jmlzone/PiPtr/doc/IMG_1385.jpg

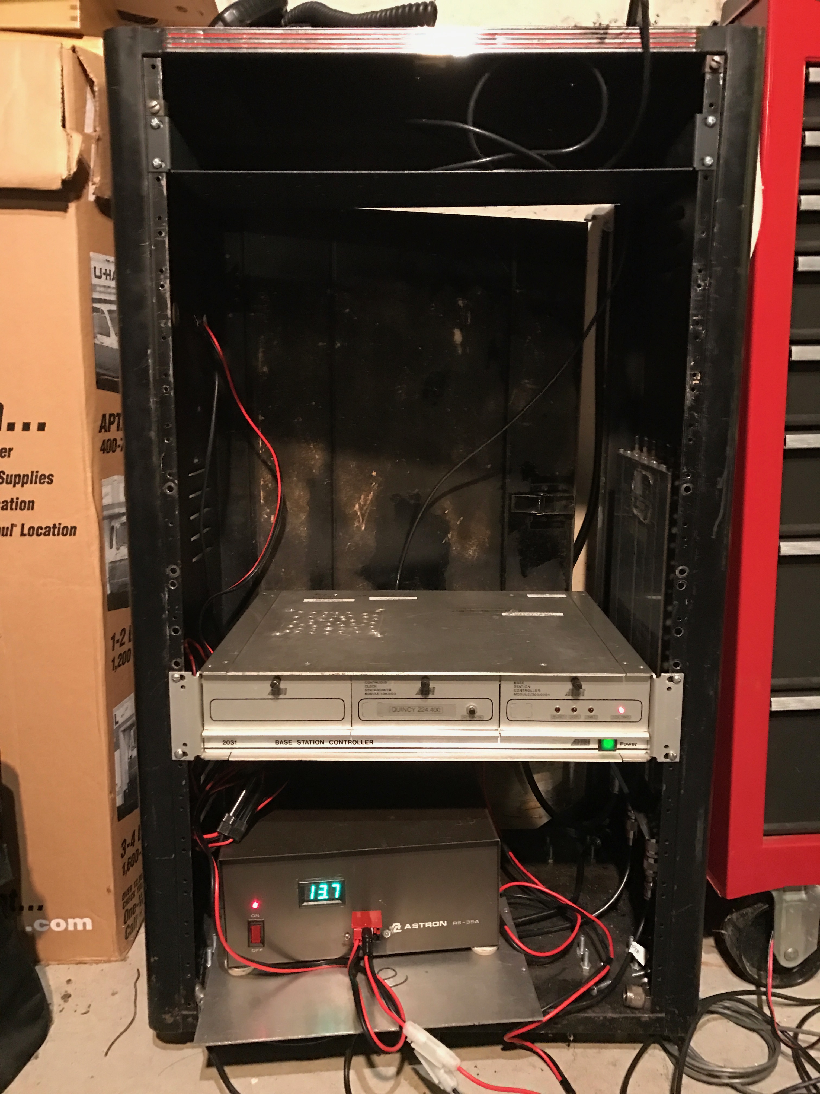
doc/IMG_1385.jpg
