jmlzone/PiPtr/doc/IMG_1389.jpg

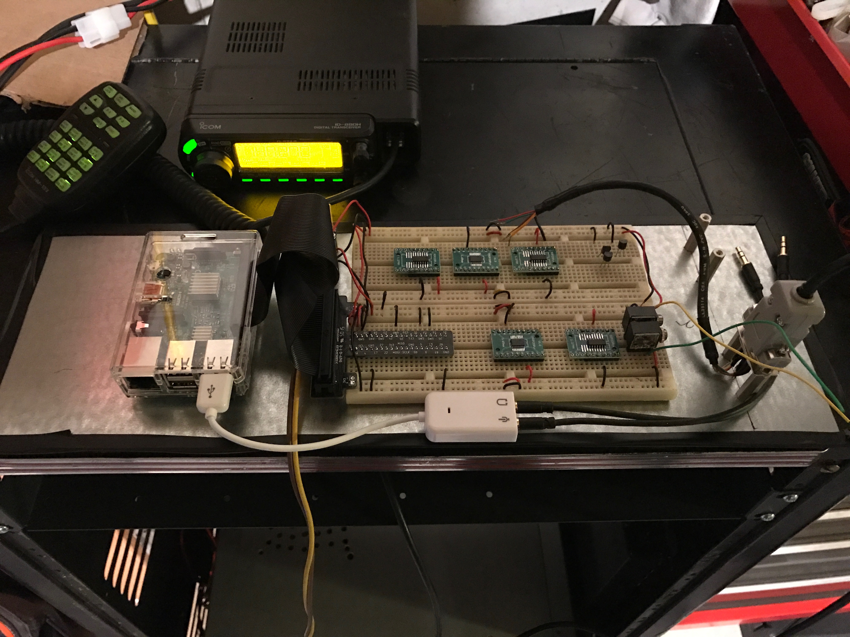
doc/IMG_1389.jpg
