jmlzone/PiPtr/doc/IMG_1816.jpg

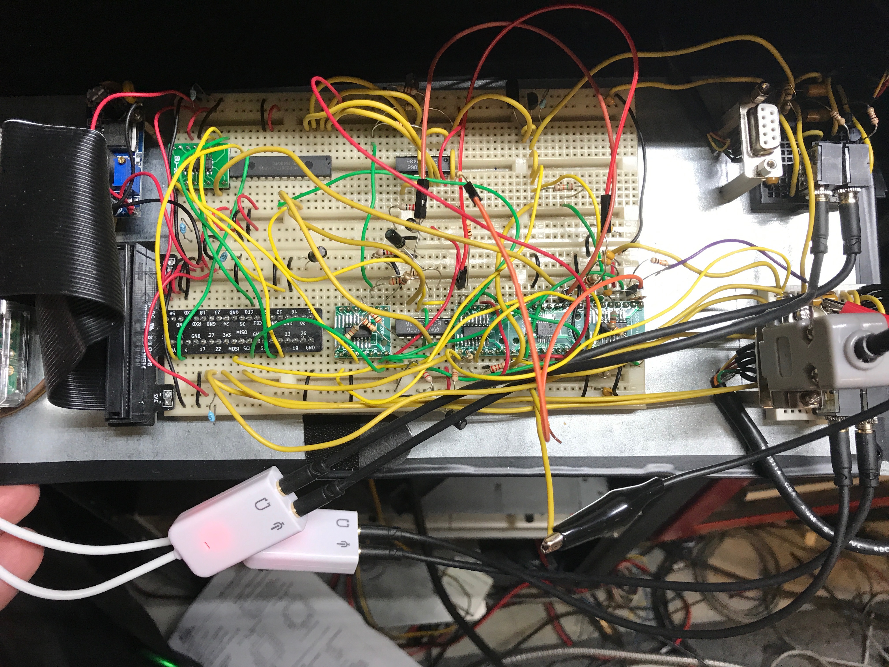
doc/IMG_1816.jpg
