jmlzone/PiPtr/python/radioPort.py

import time
import socket
import os.path
import RPi.GPIO as GPIO
import subprocess
import sys
import re
import signal
import threading
#import tail
import rptFsm
from logit import logit

from multiprocessing import Process, Value, Array, Queue
class tx:
    """ class describing a transmitter """
    def __init__(self, port):
        self.installPath = os.path.dirname(os.path.realpath(__file__))
        self.port = port # handle to parent
        self.pltone = 100.0
        self.id = "n0call"
        self.tailMsgList =  []
        self.beaconMsgList = []
        self.timeout = 3600 # 1 hour max tx up continously
        self.taildly = 0.5 # seconds
        self.txupdly = 1 # seconds When coming up to beacon, delay bedore sending
        self.hangtime = 1 #seconds
        self.idtime = 300 # seconds
        self.polite = 30
        self.disable = False
        self.TailMessagesDone = False
        self.txPinLvl = 1
        if(self.port.portnum == 1) :
            self.pttPin = 15
            self.txState=self.port.globalState.tx1.setValue
        else :
            self.pttPin = 22
            self.txState=self.port.globalState.tx2.setValue

        GPIO.setmode(GPIO.BOARD)
        GPIO.setup(self.pttPin, GPIO.OUT)
        GPIO.output(self.pttPin,(not self.txPinLvl))
        #self.tail_msg = tail.tail_msg(self.port.card)
        self.pid = False
        self.idPid = False
        self.beepMethod = 2 # 0=none, 1=tone, 2=wave 3=morse
        self.beepTone = "660 5000 30 440 5000 30 1000 5000 30"
        self.tailBeepWav = self.localPath('../sounds/Tink.wav')
        self.defMorseWpm = 20
        self.defMorseTone = 660
        self.defMorseVolume = 5000
        self.beepMorse = "20 440 5000 beep"
        self.xmlvars = ( 'pltone', 'id', 'idtime', 'polite', 'timeout',
                         'taildly', 'hangtime', 'disable', 'txupdly',
                         'txPinLvl', 'beepMethod', 'beepTone',
                         'tailBeepWav', 'beepMorse',
                         'defMorseWpm','defMorseTone','defMorseVolume'
                     ) # data to store in xml config
        self.up = False

    def localPath(self,file) :
        return (os.path.abspath(os.path.join(self.installPath,file)))
    
    def addTailMsg(self, method,msg,cancelable,isid,requeue,alt):
        self.tailMsgList.append((method,msg,cancelable,isid,requeue,alt))
        print("Added tail message %s " % msg)

    def addBeaconMsg(self, method,msg,cancelable,isid,requeue,alt):
        self.beaconMsgList.append((method,msg,cancelable,isid,requeue,alt))
        print("Added beacon message %s " % msg)


    def tx(self) :
        if( not self.disable) :
            #self.port.startPl(pltone)
            #self.port.tx_enable()
            GPIO.output(self.pttPin,self.txPinLvl)
            #self.port.gui.updateTxGui(self.port.portnum,True)
            self.txState(True,'red')
            self.up = True

    def plGen(self) :
        """ Starts this transmitters Pl generator

        not going to worry about the details yet
        """
        print("pl gen on")
    def plStop(self) :
        """ Stops this transmitters Pl generator

       not going to worry about the details yet
       """
        print("pl gen off")
        
    def down(self):
        GPIO.output(self.pttPin,(not self.txPinLvl))
        #self.port.gui.updateTxGui(self.port.portnum,False)
        self.txState(False)
        self.up = False

    def playMsgs(self,msgList) :
        print(" play messages called")
        print(msgList)
        self.cancel = False
        id_played = False
        i=0;
        while(i<len(msgList)) :
            print("i = %d" %i)
            ele = msgList[i]
            print("ele =")
            print(ele)
            (method,msg,cancelable,isid,requeue,alt) = ele
            self.cancellable = cancelable
            # run it
            if(not self.cancel or not cancelable) :
                # realy run it
                try:
                    print("Play messages Trying")
                    if(callable(method)) :
                        print("Play messages direct call")
                        if(type(msg) == type(dict())) :
                            print("with dictionary")
                            method(self.port.card,**msg)
                        else:
                            print("without dictionary")
                            method(self.port.card,msg)
                    else :
                        print("Play messages external call")
                        args = method + [self.port.card] + msg
                        print("tail message play: (args)")
                        print(args)
                        self.pid = subprocess.Popen(args)
                        self.pid.wait()
                except:
                    print("error could not run the tail message")
            if(self.cancel and alt and self.pid.returncode() <0) :
                (method,msg) = alt
                args = method + [self.port.card] + msg
                print("tail message alt play: (args)")
                print(args)
                try: 
                    self.pid = subprocess.call(args)
                except:
                    print("error could not run the alternate message")
                if(isid and (alt or (not self.cancel and not cancelable))) :
                    id_played = True
            if (not requeue):
                msgList.pop(i)
            else :
                i=i+1
        self.pid = None
        print("Play messages Exit")
        return (id_played)
 
    def sendId(self) :
        self.idPid = subprocess.Popen([self.localPath('../bin/mout'), self.port.card, '20', '660', '5000', self.id])
        self.idPid.wait()

    def tailBeep(self) :
        if(self.beepMethod == 1) : # tone
            args = [self.localPath('../bin/tout'),self.port.card] + self.beepTone.split()
            print(args)
            beepPid = subprocess.call(args)
        elif(self.beepMethod == 2) : # wave
            beepPid = subprocess.Popen(['/usr/bin/aplay', '-D', self.port.card, self.tailBeepWav])
        elif(self.beepMethod == 3) : # morse
            args = [self.localPath('../bin/mout'),self.port.card] + self.beepMorse.split()
            print(args)
            beepPid = subprocess.call(args)
        else : # none
            return

    def idRunning(self):
        if(self.idPid) :
            self.idPid.poll()
            if(self.idPid.returncode == None) :
                return True
            else :
                return False
        else :
            return True

class rx:
    """ class describing a receiver """
    def __init__(self, port, q):
        self.port = port # handle to parent port
        self.q = q
        self.rxState = 0
        self.plDet = 0
        self.idle_timer = 0
        self.busy_timer = 0
        self.kerchunk_timer = 0
        self.anti_kerchunk = False
        self.timeout = 180     # seconds
        self.resetTimeout = 1 # seconds
        self.IdleTimeout = 600 # seconds
        self.cmdTimeout = 10 # seconds
        self.muteTime = 1 # seconds
        self.disabled = False
        self.expired = False
        self.idle = True
        self.useCtcssPin = True
        self.ctcssPinLvl = 0
        self.useCorPin = True
        self.corPinLvl = 0
        self.deemp = False
        self.descEn = False
        self.portDet = False
        self.rxActive = threading.Event()
        self.useSoftCtcss = False
        self.ctcssAct = [ 0, 0, 0, 0, 0, 0, 0, 0]
        self.softCtcssAllow = [ 0, 0, 0, 0, 0, 0, 0, 0]
        self.softCtcssCmd   = [ 0, 0, 0, 0, 0, 0, 0, 0]
        self.cmdMode = False
        self.audioEnable = True
        if(self.port.portnum == 1) :
            self.corPin = 11
            self.ctcssPin = 13
            self.corState=self.port.globalState.cor1.setValue
            self.ctcssState=self.port.globalState.ctcss1.setValue
            self.cmdState=self.port.globalState.cmd1.setValue
            self.softCtcssState=self.port.globalState.softCtcss1.setValue
        else :
            self.corPin = 16
            self.ctcssPin = 18
            self.corState=self.port.globalState.cor2.setValue
            self.ctcssState=self.port.globalState.ctcss2.setValue
            self.cmdState=self.port.globalState.cmd2.setValue
            self.softCtcssState=self.port.globalState.softCtcss2.setValue
        GPIO.setmode(GPIO.BOARD)
        GPIO.setup(self.ctcssPin, GPIO.IN, pull_up_down=GPIO.PUD_UP)
        GPIO.setup(self.corPin, GPIO.IN, pull_up_down=GPIO.PUD_UP)
        self.xmlvars = ('timeout', 'resetTimeout', 'IdleTimeout', 'disabled',
                        'useCtcssPin', 'ctcssPinLvl', 'useCorPin', 'corPinLvl',
                        'deemp', 'descEn', 'portDet',
                        'useSoftCtcss', 'softCtcssAllow', 'softCtcssCmd',
                        'cmdMode', 'cmdTimeout', 'muteTime')

    def ctcss(self):
        if(GPIO.input(self.ctcssPin) == self.ctcssPinLvl) :
            rx = True
        else :
            rx = False
        return(rx)

    def active(self):
        if(GPIO.input(self.corPin) == self.corPinLvl or self.useCorPin == False) :
            if(self.useCtcssPin):
                rx=self.ctcss()
            else:
                rx = True
        else :
            rx = False
        return(rx)

    def update(self,channel): # for when called by GPIO interrupt
        ctcssCmd = False
        softCtcss = False
        if(self.useSoftCtcss) :
            for i in range(8) :
                if( self.ctcssAct[i] and self.softCtcssAllow[i] ) :
                     softCtcss = True
                if( self.ctcssAct[i] and self.softCtcssCmd[i] ) :
                    ctcssCmd = True
        if(softCtcss or self.useSoftCtcss == False):
            rx = self.active() or softCtcss
        else:
            rx = False
        rx = rx and not self.disabled
        if(rx != self.rxState) :
            if(rx) :
                self.rxActive.set()
                self.port.fsm.rxTimer.reset()
                self.port.fsm.rxIdleTimer.stop()
            else :
                self.rxActive.clear()
                if (self.port.cmd != "") :
                    self.q.put(" ")
            self.rxState = rx
        if(ctcssCmd) :
           self.cmdModeSet()
           self.port.fsm.cmdTimer.reset()
        self.port.fsm.updateRx(rx)
        #self.port.gui.updateRxGui(self.port.portnum,(GPIO.input(self.corPin) == self.corPinLvl),
        #            (GPIO.input(self.ctcssPin) == self.ctcssPinLvl),self.ctcssAct)
        self.corState(GPIO.input(self.corPin) == self.corPinLvl)
        self.ctcssState(GPIO.input(self.ctcssPin) == self.ctcssPinLvl)
    def cmdModeSet(self):
        if(not self.cmdMode) :
            self.cmdState(True,'yellow')
            self.cmdMode = True
    def cmdModeClr(self):
        if(self.cmdMode) :
            self.cmdState(False,'yellow')
            self.cmdMode = False
    def softDecode (self,q):
        mmPath = self.port.tx.localPath('../bin/multimon')
        if(self.port.hwio.checkCard(self.port.card)) :
            logit("Port %d : starting multimon %s on %s" % (self.port.portnum, mmPath, self.port.card)) 
            try:
                p=subprocess.Popen([mmPath, self.port.card, '-a', 'dtmf', '-a', 'ctcss'], stdout=subprocess.PIPE)
            except:
                # dummy test wrapper to simulate multimon
                import io
                class dummy:
                    def __init__(self):
                        self.stdout=io.StringIO("DTMF: 1")
                    p=dummy()

            time.sleep(1)
            while(self.port.enabled and (p.poll()==None)) :
                txt = str(p.stdout.readline())
                ctcss = re.search(r'CTCSS (?P<state>[DL]): (?P<num>\d)',txt)
                dtmf = re.search(r'DTMF: (?P<tone>[0123456789ABCDEF])',txt)
                mute = re.search(r'MUTE',txt)
                if(ctcss != None) :
                    #print( txt )
                    self.ctcssAct[int(ctcss.group('num'))] = (ctcss.group('state') == 'D')
                    #print( self.ctcssAct )
                    self.update(False) # update the RX status
                    self.softCtcssState(self.ctcssAct)
                if(dtmf != None) :
                    q.put(dtmf.group('tone'))
                if(self.port.rx.cmdMode) :
                    self.port.fsm.cmdTimer.reset()
                    self.port.fsm.mute()
            # while exits when port disabled
            p.terminate()
            #join(self.sd,None)
        else:
            print("Error, bad card %s for soft decode, check config or run port detect", self.port.card)

    def run(self) :
        self.sd = threading.Thread(target=self.softDecode, args=[self.q])
        self.sd.daemon = True
        self.sd.start()
        if(self.useCorPin) :
            GPIO.add_event_detect(self.corPin, GPIO.BOTH, callback=self.update)
        if(self.useCtcssPin) :
            GPIO.add_event_detect(self.ctcssPin, GPIO.BOTH, callback=self.update)


class radioPort :
    """ The port class has a reciever and a transmitter and houses any common data 
    it has multiple threads.
    The soft deode thread runs multimon to decode PL and DTMF
    The ctcss pin and cor pins are handled by interups.
    """
    def __init__(self, portnum,q, globalState) :
        self.portnum = portnum
        if(portnum == 1 ) :
            self.card = "sysdefault:CARD=Device"
        elif (portnum == 2 ) :
            self.card = "sysdefault:CARD=Device_1"
        else :
            self.card = "sysdefault"
        
        self.isLink = False
        self.linkState = 0
        self.q = q
        self.globalState = globalState
        self.rx = rx(self,q) # self passed in is the port instance for parent refences to this data
        self.tx = tx(self)
        self.fsm = rptFsm.rptFsm(self)
        self.xmlvars = ( 'card', 'isLink', 'linkState', 'enabled', 'idleWav')
        self.cmd = ""
        self.enabled = True
        self.idleWav = self.tx.localPath('../sounds/idle.wav')
        self.fsmThread = None
        self.cmdThread = None
        

        
    def run(self) :
        if(self.enabled) :
            self.rx.run()
            self.fsm.startUp()
            #threading.Thread.join(self.fsmThread,None)
            
    def setLinkState(self,linkNum):
        if(linkNum >3) :
            linkNum = 0;
        if(self.linkState) :
            if(self.fsm.linkVotes) :
                self.fsm.linkVotes = 0;  #If we were linked clear our vote.
            if((self.linkState==1) & (self.other.linkState==1) & self.other.enabled) :
                self.other.fsm.clrLinkRx(1) # port 1 linking is special and software only
                self.fsm.clrLinkRx(1) # clear ourself also
        self.linkState = linkNum;
        self.hwio.WritePGAChan(linkNum,self.portnum+4,0)
        self.hwio.WritePGAGain(self.hwio.gain[linkNum][linkNum],self.portnum+4,0)
        if(self.fsm.rxState == 'rx') :
            self.fsm.rxup() # re establish link state
            
